Batterhead221/ESP32-C6_MICROCONTROLLER/outputs/img/fab.jpeg

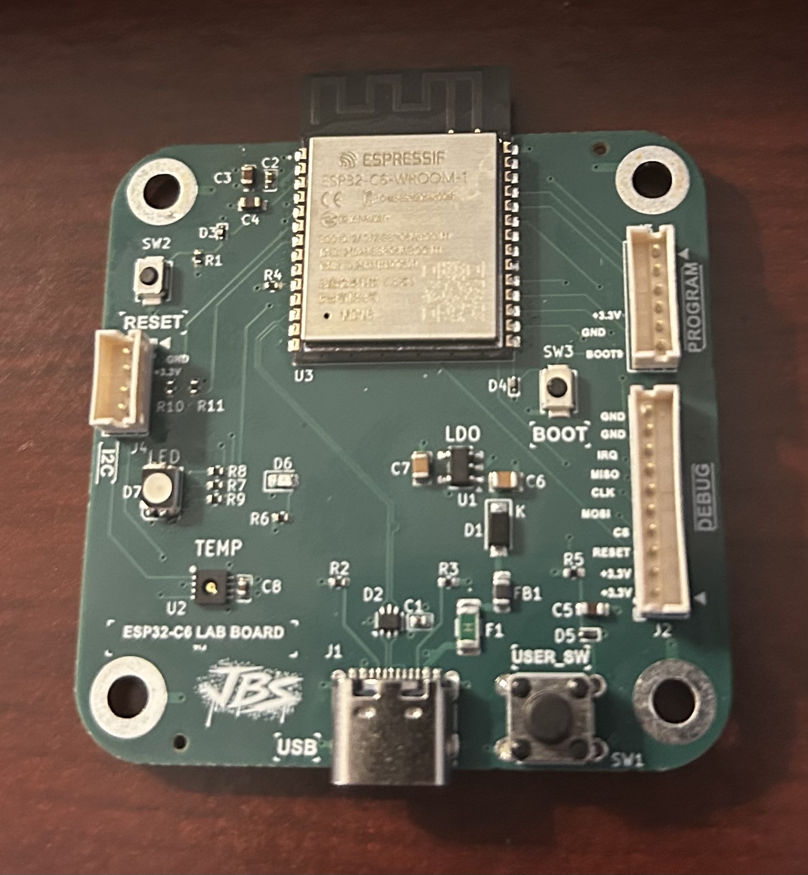
outputs/img/fab.jpeg
