Batterhead221/ESP32-C6_MICROCONTROLLER/outputs/img/bring-up/bring-up-2.jpeg

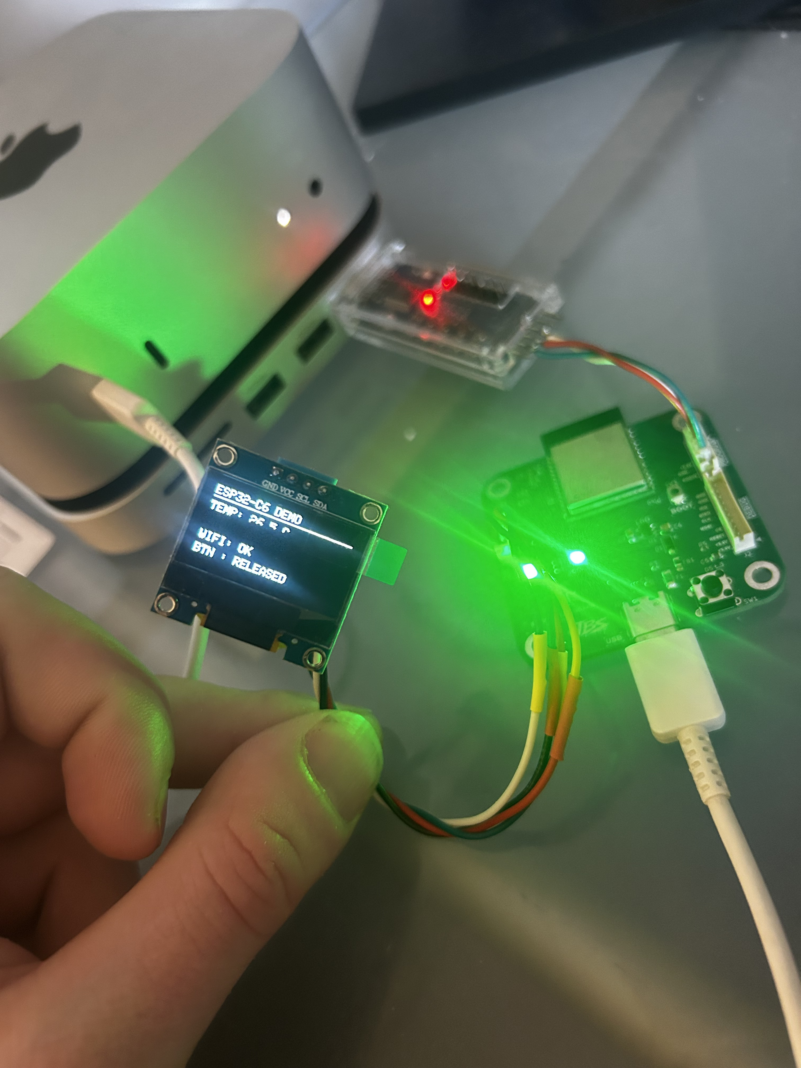
outputs/img/bring-up/bring-up-2.jpeg
