Batterhead221/ESP32-C6_MICROCONTROLLER/Outputs/IMG/Bring-Up/Bring_Up-1.jpeg

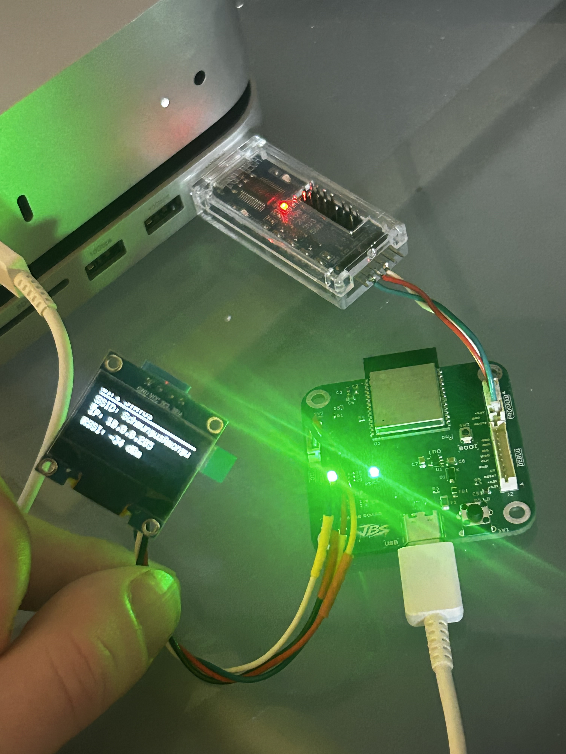
Outputs/IMG/Bring-Up/Bring_Up-1.jpeg
